koNrand/drone-o-tron/LTSpice_Simulation.asc

C1: cap; 20n
C3: cap; 100n
C4: cap; 10n
C5: cap; 10n
D1: schottky; 1N5819
D2: schottky; 1N5819
Q1: npn
R1: res; 1k
R2: res; 10k
R3: res; 10k
R4: res; 10k
R5: res; 1k
R6: res; 10k
R7: res; 2k
R8: res; 1k
R9: res; 1k
R10: res; {timbre*100k+1}
R11: res; {(1-timbre)*100k+1}
R12: res; {cutoff*100k+1}
R13: res; {cutoff*100k+1}
R14: res; 1k
R15: res; 35k
R16: res; {resonance*100k+1}
R17: res; 1k
R18: res; 1k
R19: res; 1k
R20: res; 1k
R21: res; 1k
R22: res; 1k
R23: res; 1k
R24: res; 1k
R25: res; 1k
R26: res; 1k
R27: res; 1.3k
R28: res; 8.7k
R29: res; 5.7k
R30: res; 4.3k
R31: res; 1k
R_Poti_1: res; {(1-tastgrad)*10k+1}
R_Poti_2: res; {10k*tastgrad+1}
U1: NE555
U2: OP07
U3: OP07
U4: OP07
U5: OP07
U6: OP07
U7: OP07
U8: OP07
V1: voltage; 3
Named nets: 0, VDD, V_M, OUT, V_up, V_down
.tran 5
.param tastgrad 1
f_min @ CV = 2.6V  ~70Hz
f_max @ CV = 1.1V ~ 5.7kHz
Tastgradpotentiometer (0%-50%)
.
Duty cycle potentiometer (0%-50%)
3V Spannungsversorgung durch zwei
in Reihe geschaltete AAA-Batterien
.
3V Voltage Source by two AAA
batteries in series
Erzeugung niederohmige 
Mittenspannung
.
creation of a low
impedance middle voltage
.param timbre 0.5
R12/R13 stereo potentiometer
für Cutofffrequenz des Filters
.
R12/R13 stereo potentiometer
for filter cutoff
timbre potentiometer - fließender
Übergang zw. Dreieck und Rechteck
.
potentiometer to sweep between 
triangle and rectangle
R16 - Potentiometer, um Resonanz 
des Filters einzustellen
.
resonance potentiometer
.param resonance 0.1
.param cutoff 0
Ausgang geht zu einer Monoklinke und einem Klasse 
A-Verstärker, welcher einen Buzzer betreibt.
.
Mono Output, alos goes to an class A Amplifier to 
run a buzzer as speaker
Klaviatur
keyboard
Kontaktkabel, mit welchem 
auf die 'Tasten' gedrückt wird.
.
Contact cable which is used
to press the 'keys'
Potentiometer, um 
f_min einzustellen
.
potentiometer to
set f_min
Potentiometer, um
f_max einzustellen
.
potentiometer to 
set f_max
DE:
einstimmiger Minisynthesizer mit Ribbonklaviatur, welcher über ein 
Monoaudiokabel gesteuert wird.
.
Es gibt: 
-zwei Trimpoteniometer, um Feinjustierungen der Maximal- 
und Minimaltonhöhe vorzunehmen.
-Potentiomter, um Tastgrad des Signals zu verändern (0-50%)
-Potentiometer für Fade zwischen Dreieck- und Rechtecksignal
-Potentiometer für Knickfrequenz eines 2-Pol-Tiefpassfilters
-Potentiometer, um Resonanz des Filters zu ändern
.
Der NPN-BJT Q1 hat die Aufgabe, den NE555 ein- und auszuschalten.
(als krude Hüllkurve - der Ton kommt nur, wenn eine Taste gedrückt wird)
Durch die Idealistät des NE555-Models kann bei der Verschaltung von Q1 
LTSpice keine Startbedingung finden,weshalb der IC direkt an GND 
hängt und nicht an Q1.
.
Die Wahl einiger Zeitkonstanten scheint vielleicht nicht sinnvoll, zielt
 aber auf eine Effizienz bei der Simulationszeit ab.
.wave "output.wav" 24 44.1k OUT
ENG:
Single-voice mini synthesizer with ribbon keyboard, controlled via a 
 mono audio cable.
.
There are: 
-two trimpoteniometers to make fine adjustments to the maximum 
and minimum pitch.
-potentiometers to change the duty cycle of the signal (0-50%).
-potentiometer for fade between triangular and rectangular signal
-potentiometer for cutoff frequency of a 2-pole low-pass filter
-potentiometer to change resonance of the filter
.
The NPN-BJT Q1 has the task of switching the NE555 on and off.
(as a crude envelope - sound only comes when there's a key pressed)
Due to the idealistic nature of the NE555 model in LTSPice, with the
 connection of Q1 LTSpice cannot find a start condition, which is why
 the IC is connected directly to GND and not via Q1.
.
The choice of some of the time constants doesn't seem usefull, but is
 due to efficiency in simulation-time.
@heissklebepanzer presents:
